shmuelzon/esphome-projects/doc/barcode_scanner/barcode_unknown.png

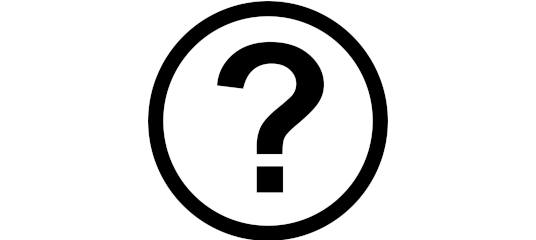
doc/barcode_scanner/barcode_unknown.png
